dmeprojects/Classpert_GreenTurtles_FinalProject/docs/Aim-A-Lyzer Hierarchie of control (1).png

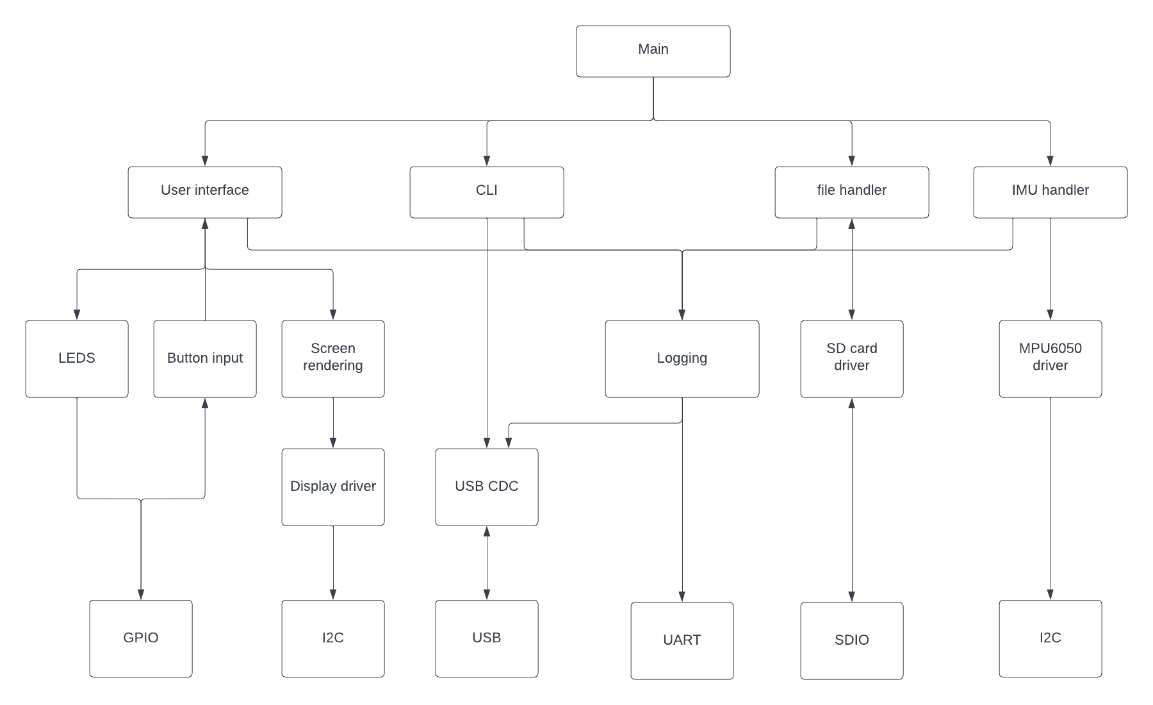
docs/Aim-A-Lyzer Hierarchie of control (1).png
