dmeprojects/Classpert_GreenTurtles_FinalProject/docs/Software block diagram.png

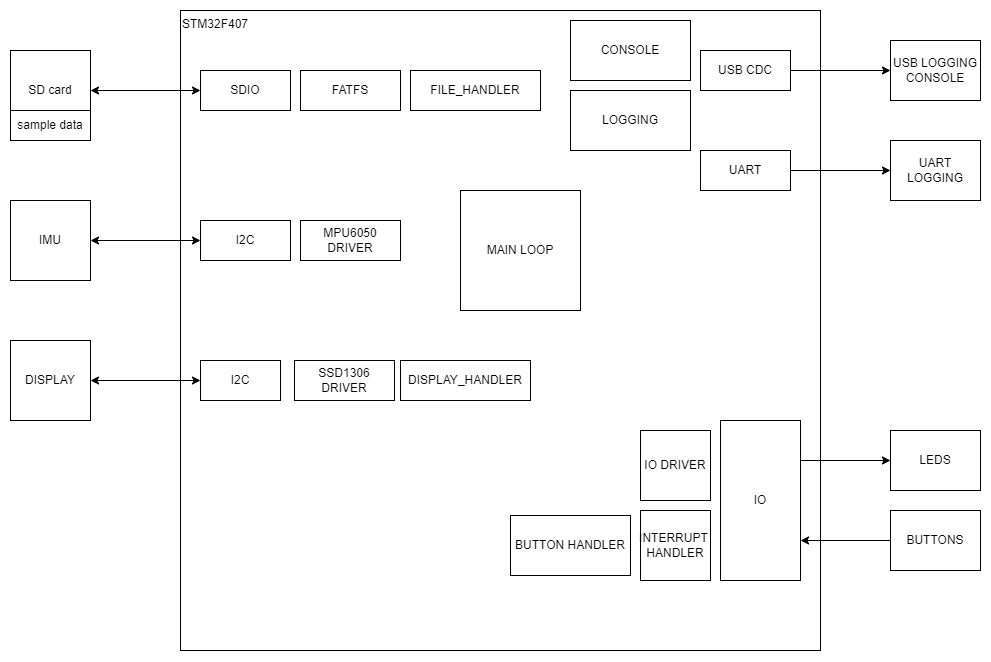
docs/Software block diagram.png
