dmeprojects/Classpert_GreenTurtles_FinalProject/Final project/Firmware/images/BlockDiagram_LEDBLINK.png

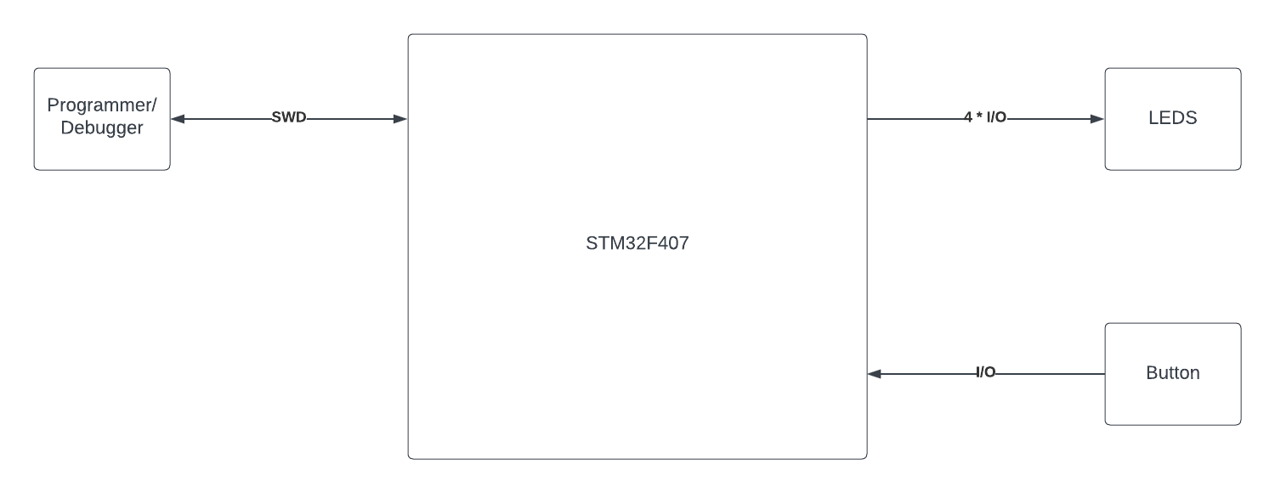
Final project/Firmware/images/BlockDiagram_LEDBLINK.png
