dmeprojects/Classpert_GreenTurtles_FinalProject/Scripts/ReadGraph/meas_files/dry_shots/MEASUREMENT_002.png

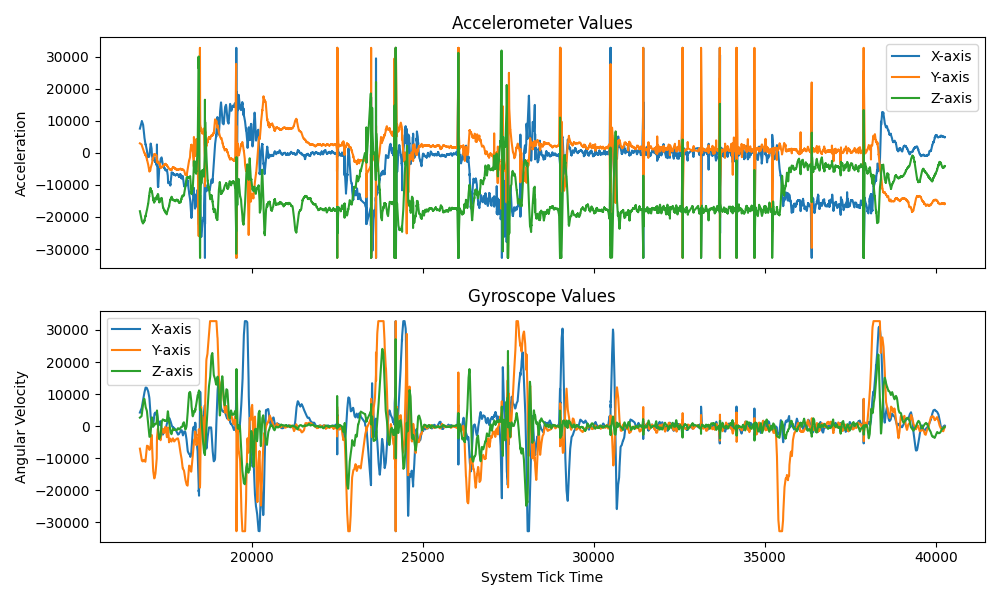
Scripts/ReadGraph/meas_files/dry_shots/MEASUREMENT_002.png
