dmeprojects/Classpert_GreenTurtles_FinalProject/Scripts/ReadGraph/meas_files/dry_shots/MEASUREMENT_005.txt.png

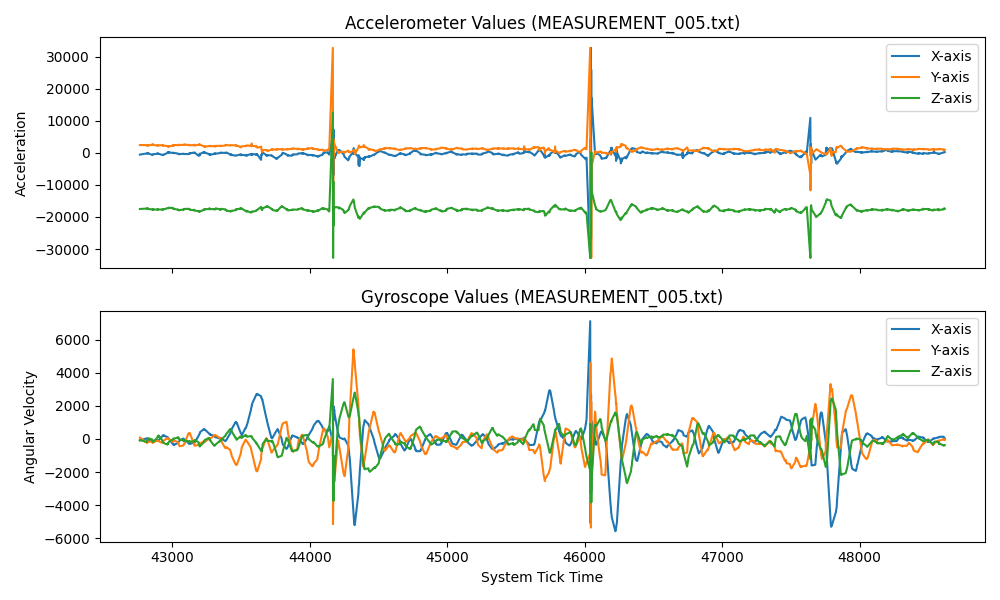
Scripts/ReadGraph/meas_files/dry_shots/MEASUREMENT_005.txt.png
