dmeprojects/Classpert_GreenTurtles_FinalProject/Scripts/ReadGraph/meas_files/live rounds/MEASUREMENT_008.png

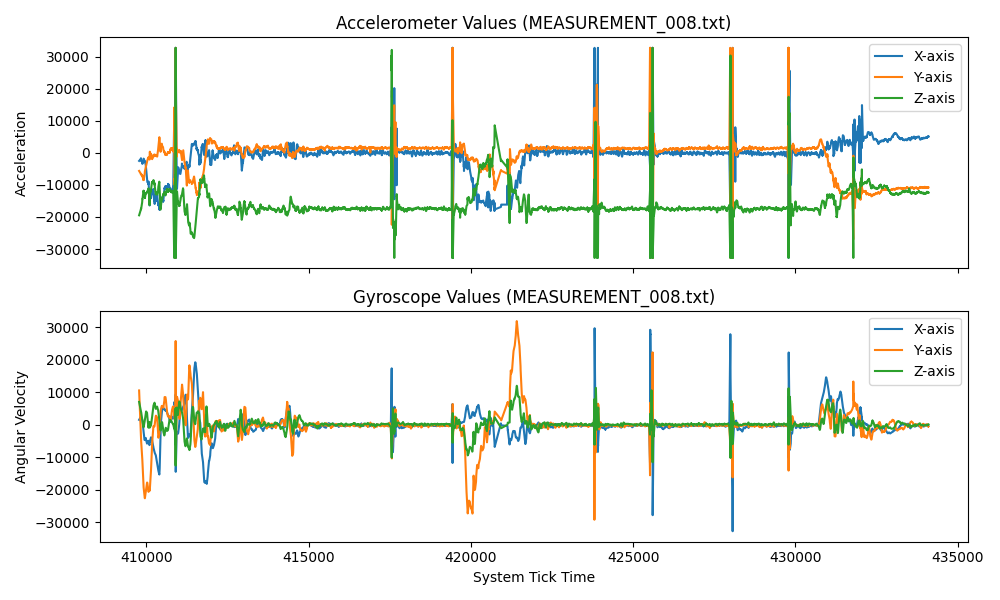
Scripts/ReadGraph/meas_files/live rounds/MEASUREMENT_008.png
