dmeprojects/Classpert_GreenTurtles_FinalProject/Scripts/ReadGraph/meas_files/live rounds/MEASUREMENT_009.png

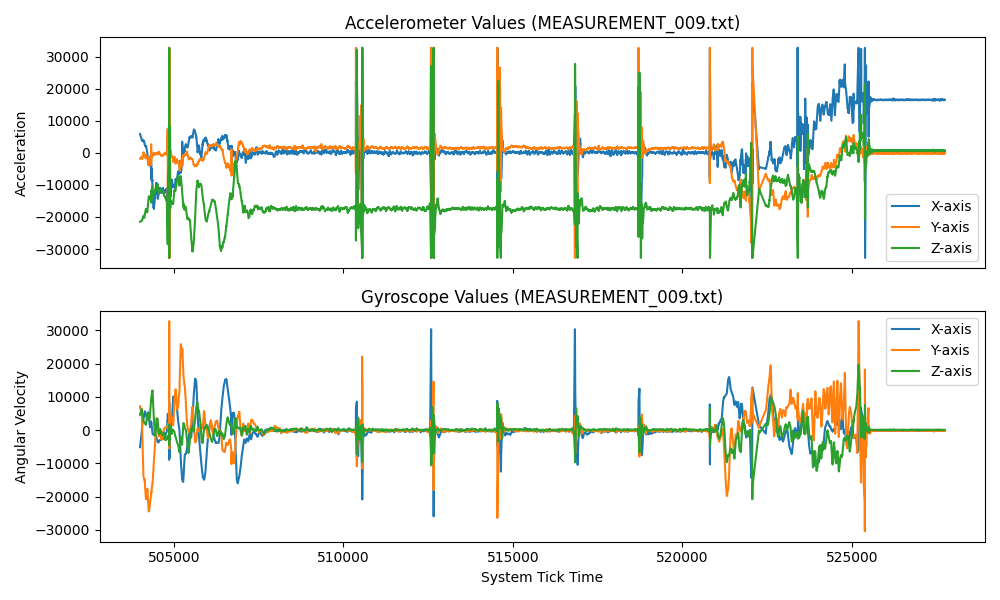
Scripts/ReadGraph/meas_files/live rounds/MEASUREMENT_009.png
