dmeprojects/Classpert_GreenTurtles_FinalProject/Scripts/ReadGraph/meas_files/live rounds/MEASUREMENT_012.png

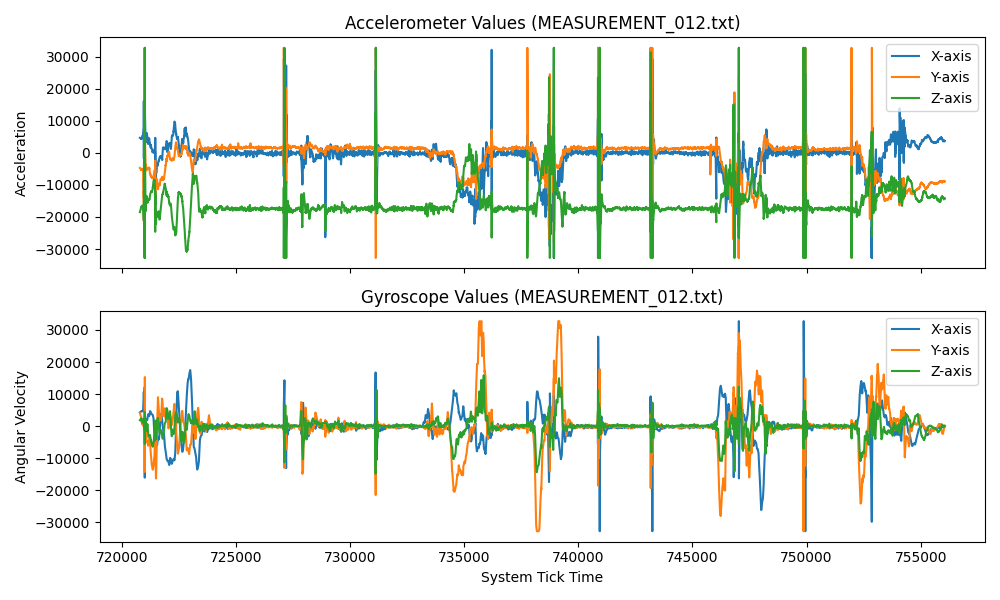
Scripts/ReadGraph/meas_files/live rounds/MEASUREMENT_012.png
