dmeprojects/Classpert_GreenTurtles_FinalProject/Scripts/ReadGraph/meas_files/MEASUREMENT_006.png

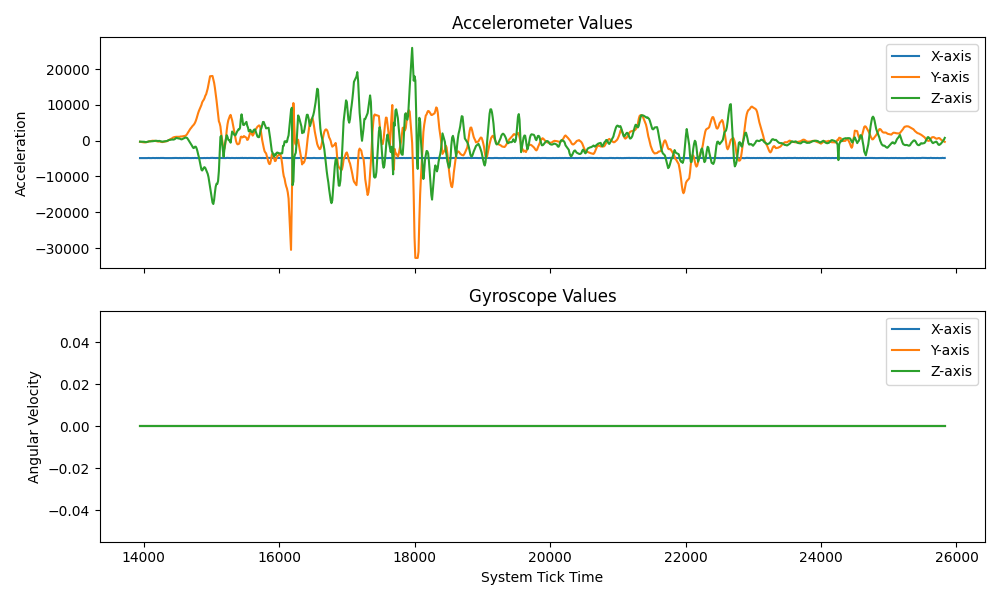
Scripts/ReadGraph/meas_files/MEASUREMENT_006.png
