dmeprojects/Classpert_GreenTurtles_FinalProject/Final project/Firmware/Application/Inc/asciHeader.h

/*
 * asci_header.h
 *
 *  Created on: Jan 4, 2024
 *      Author: nick_
 */

#ifndef INC_ASCIHEADER_H_
#define INC_ASCIHEADER_H_


#define ASCIART_1 "█████╗ ██╗███╗   ███╗       █████╗       ██╗  ██╗   ██╗███████╗███████╗██████╗ \n\r"
#define ASCIART_2 "██╔══██╗██║████╗ ████║      ██╔══██╗      ██║  ╚██╗ ██╔╝╚══███╔╝██╔════╝██╔══██╗\n\r"
#define ASCIART_3 "███████║██║██╔████╔██║█████╗███████║█████╗██║   ╚████╔╝   ███╔╝ █████╗  ██████╔╝\n\r"
#define ASCIART_4 "██╔══██║██║██║╚██╔╝██║╚════╝██╔══██║╚════╝██║    ╚██╔╝   ███╔╝  ██╔══╝  ██╔══██╗\n\r"
#define ASCIART_5" ██║  ██║██║██║ ╚═╝ ██║      ██║  ██║      ███████╗██║   ███████╗███████╗██║  ██║\n\r"
#define ASCIART_6" ╚═╝  ╚═╝╚═╝╚═╝     ╚═╝      ╚═╝  ╚═╝      ╚══════╝╚═╝   ╚══════╝╚══════╝╚═╝  ╚═╝\n\r"
#define ASCIART_7"\n\r\n\r"





#endif /* INC_ASCIHEADER_H_ */
