dmeprojects/Classpert_GreenTurtles_FinalProject/Final project/Firmware/Application/Src/consoleIO.c

// Console IO is a wrapper between the actual in and output and the console code
// In an embedded system, this might interface to a UART driver.

#include "consoleIo.h"
#include <stdio.h>

#include "usb_device.h"

#include "usbCom.h"
#include "string.h"

eConsoleError ConsoleIoInit(void)
{
	return CONSOLE_SUCCESS;
}

// This is modified for the Wokwi RPi Pico simulator. It works fine
// but that's partially because the serial terminal sends all of the
// characters at a time without losing any of them. What if this function
// wasn't called fast enough?
//eConsoleError ConsoleIoReceive(uint8_t *buffer, const uint32_t bufferLength, uint32_t *readLength)
//{
//	uint32_t i = 0;
//	char ch;
//
//	while (uart_is_readable(uart0))
//	{
//  	ch = uart_getc(uart0);
//  	uart_putc(uart0, ch); // echo
//		buffer[i] = (uint8_t) ch;
//		i++;
//	}
//
//	*readLength = i;
//	return CONSOLE_SUCCESS;
//}

eConsoleError ConsoleIoReceive(uint8_t *buffer, const uint32_t bufferLength, uint32_t *readLength)
{
	uint32_t i = 0;
	//char ch;

	//Read USB buffer
	//CDC_Receive_FS(&lBuffer, &LengthReceived);

	if (usbCom.comReady)
	{
		for( i = 0; i< usbCom.bufferLength; i++)
		{
			buffer[i] = usbCom.comBuffer[i];
		}

		*readLength = usbCom.bufferLength;

		usbCom.comReady = 0;
	}
	else
	{
		buffer = NULL;
		*readLength = 0;
	}
	return CONSOLE_SUCCESS;

}

eConsoleError ConsoleIoSendString(const char *buffer)
{
	//printf("%s", buffer);

	uint16_t length = 0;
	uint8_t usbStatus = USBD_OK;

	length = strlen(buffer);

	usbStatus = CDC_Transmit_FS(buffer, length);

	if (usbStatus == USBD_OK)
	{
		return CONSOLE_SUCCESS;
	}
	else
	{
		return CONSOLE_ERROR;
	}

}
